markusdeli/Adobe-Lightroom-MIDI-Controller/3D-models/1MODE.stl

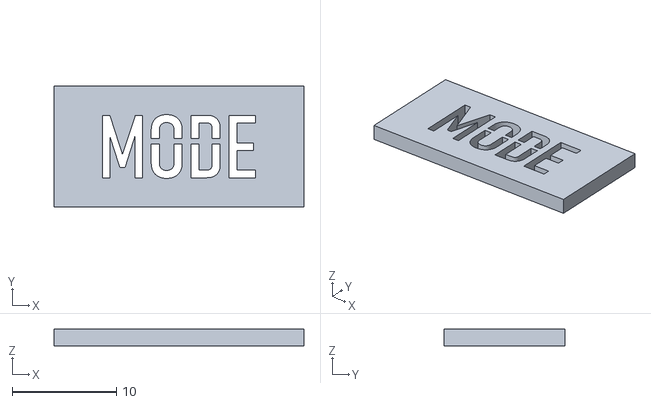
[picture p15: CAD file, 2021-11-03]
3D-models/1MODE.stl
24.0 x 11.6 x 1.60
