markusdeli/Adobe-Lightroom-MIDI-Controller/3D-models/DongleBottom.stl

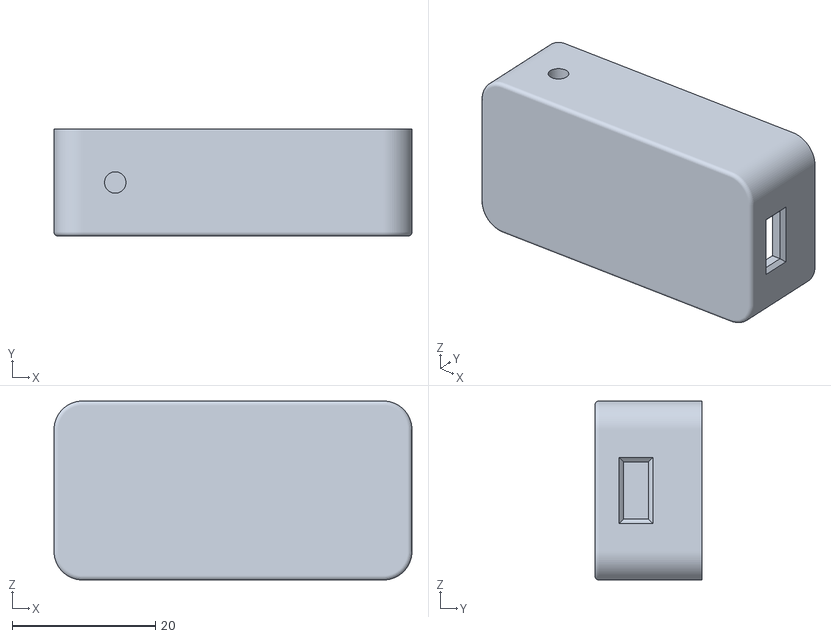
[picture p16: CAD file, 2021-11-03]
3D-models/DongleBottom.stl
50.0 x 15.0 x 25.0
