markusdeli/Adobe-Lightroom-MIDI-Controller/3D-models/color encoder.stl

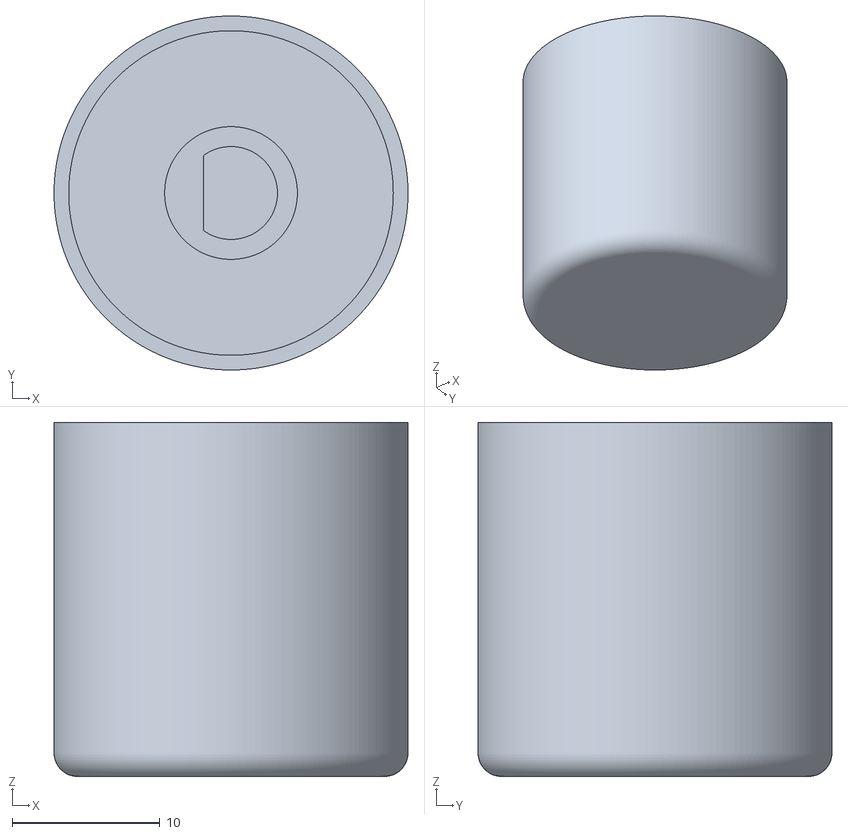
[picture p17: CAD file, 2021-11-03]
3D-models/color encoder.stl
24.0 x 24.0 x 24.0
