markusdeli/Adobe-Lightroom-MIDI-Controller/3D-models/kabelkammmidi.stl

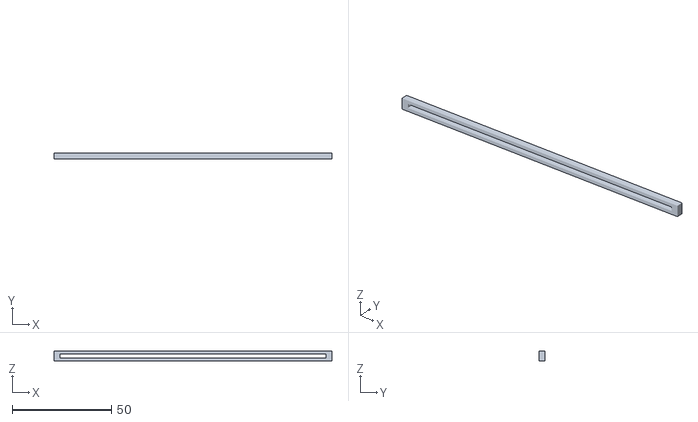
[picture p18: CAD file, 2021-11-03]
3D-models/kabelkammmidi.stl
140.0 x 3.00 x 5.00
