markusdeli/Adobe-Lightroom-MIDI-Controller/3D-models/1M2.stl

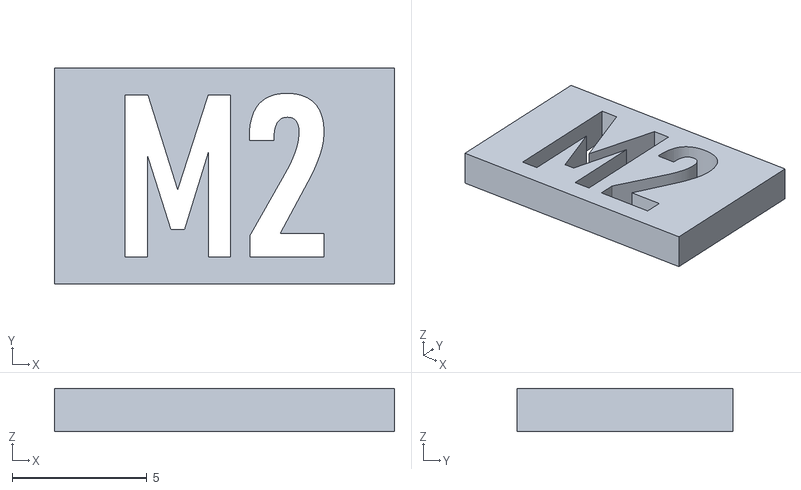
[picture p19: CAD file, 2021-11-03]
3D-models/1M2.stl
12.6 x 8.00 x 1.60
