markusdeli/Adobe-Lightroom-MIDI-Controller/3D-models/encoderfillMIDI.stl

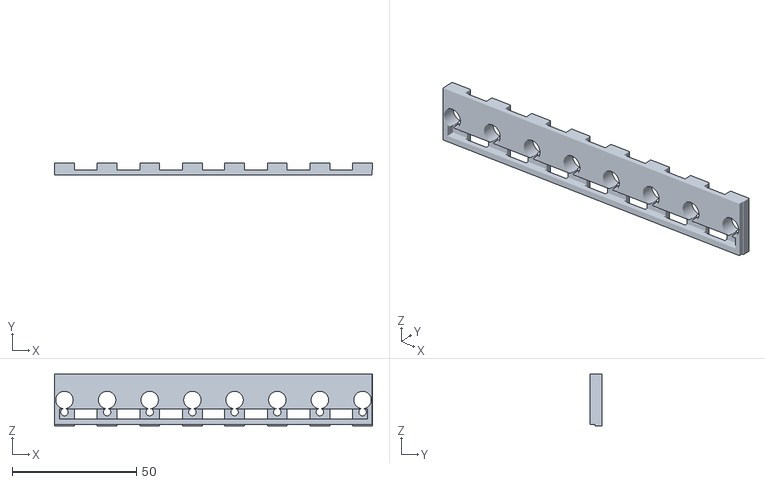
[picture p20: CAD file, 2021-11-03]
3D-models/encoderfillMIDI.stl
127.9 x 5.00 x 20.7
