markusdeli/Adobe-Lightroom-MIDI-Controller/3D-models/midicasetop.stl

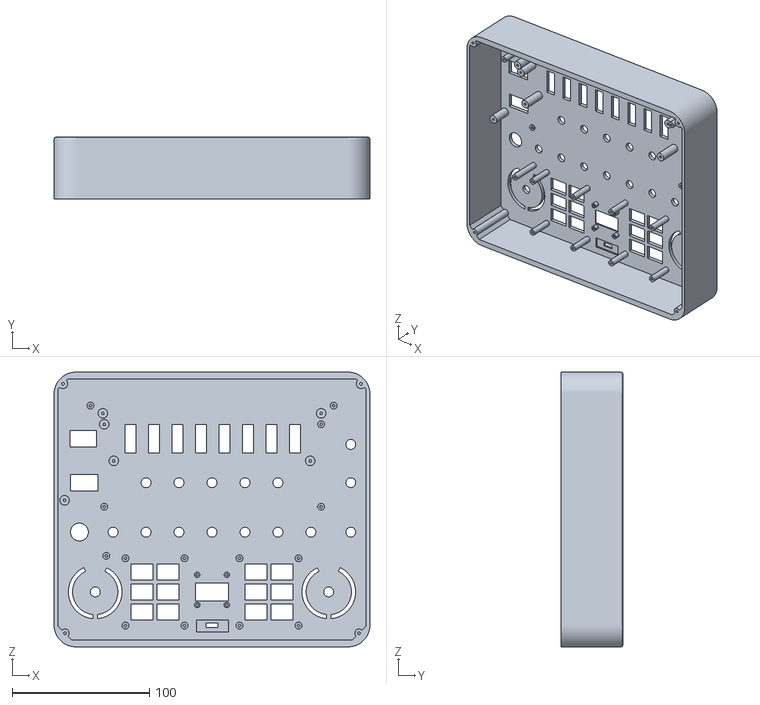
[picture p21: CAD file, 2021-11-03]
3D-models/midicasetop.stl
230.0 x 45.0 x 200.0
