markusdeli/Adobe-Lightroom-MIDI-Controller/3D-models/encoderbracketmidi.stl

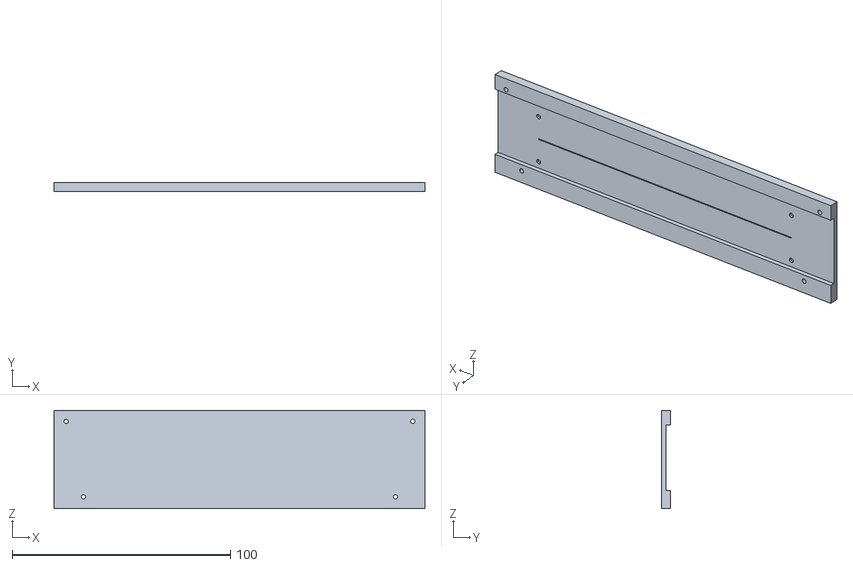
[picture p22: CAD file, 2021-11-03]
3D-models/encoderbracketmidi.stl
170.0 x 4.00 x 45.0
