markusdeli/Adobe-Lightroom-MIDI-Controller/3D-models/mouseshaftMIDI.stl

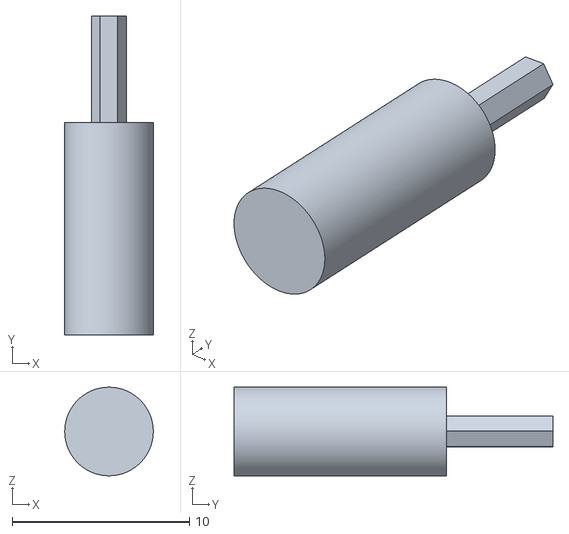
[picture p23: CAD file, 2021-11-03]
3D-models/mouseshaftMIDI.stl
5.00 x 18.0 x 5.00
