markusdeli/Adobe-Lightroom-MIDI-Controller/3D-models/DongleTop.stl

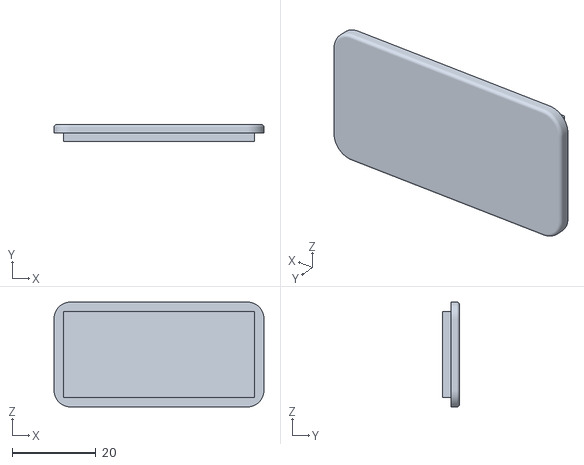
[picture p24: CAD file, 2021-11-03]
3D-models/DongleTop.stl
50.0 x 4.00 x 25.0
