markusdeli/Adobe-Lightroom-MIDI-Controller/3D-models/encoderKnobMaxiMIDI.stl

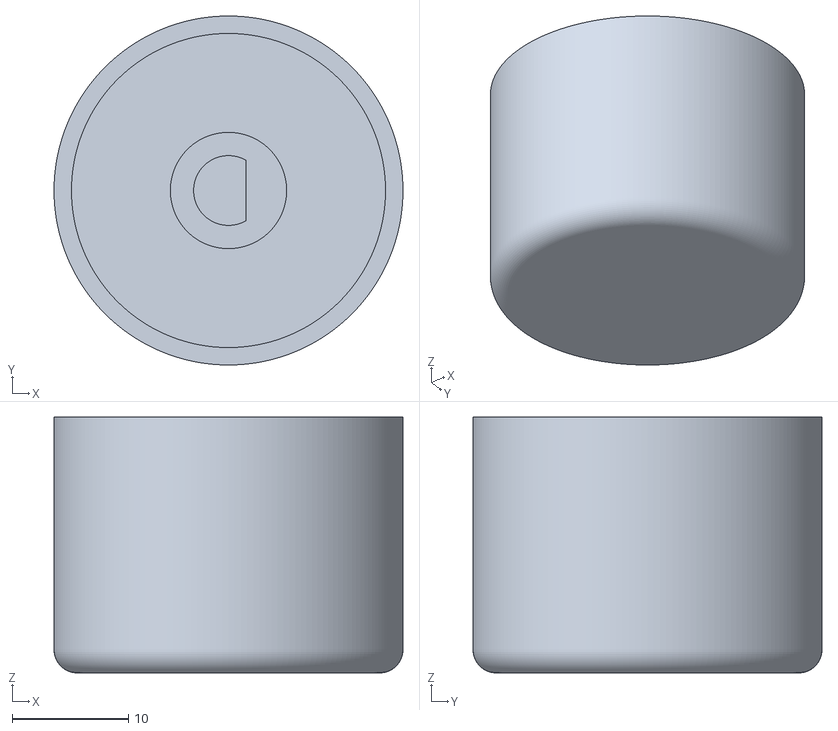
[picture p25: CAD file, 2021-11-03]
3D-models/encoderKnobMaxiMIDI.stl
30.0 x 30.0 x 22.0
