markusdeli/Adobe-Lightroom-MIDI-Controller/3D-models/midicontrollerv1.stl

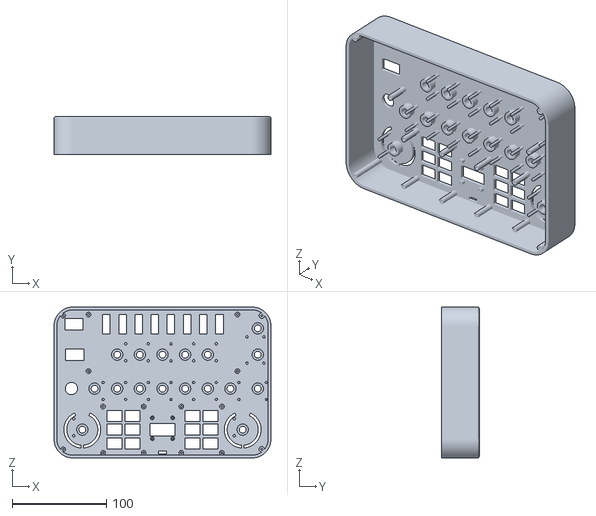
[picture p26: CAD file, 2021-11-03]
3D-models/midicontrollerv1.stl
230.0 x 40.0 x 160.0
