markusdeli/Adobe-Lightroom-MIDI-Controller/3D-models/b2.stl

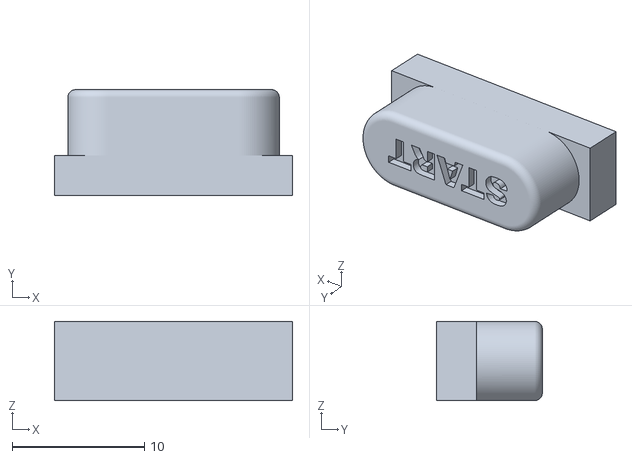
[picture p27: CAD file, 2021-11-03]
3D-models/b2.stl
18.0 x 8.00 x 6.00
