markusdeli/Adobe-Lightroom-MIDI-Controller/3D-models/stütze buttonMIDI.stl

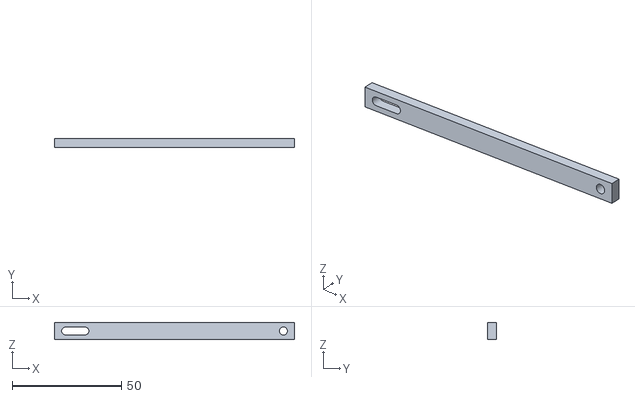
[picture p28: CAD file, 2021-11-03]
3D-models/stütze buttonMIDI.stl
110.0 x 4.00 x 8.00
