markusdeli/Adobe-Lightroom-MIDI-Controller/3D-models/buttonRotary.stl

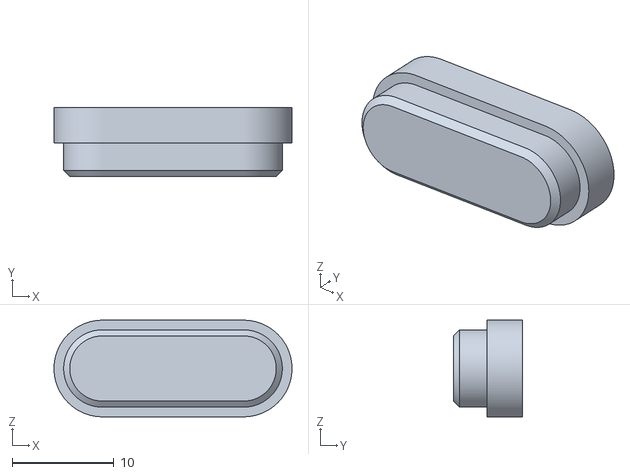
[picture p29: CAD file, 2021-11-03]
3D-models/buttonRotary.stl
23.4 x 6.80 x 9.50
