markusdeli/Adobe-Lightroom-MIDI-Controller/3D-models/buttonnichtsoklein.stl

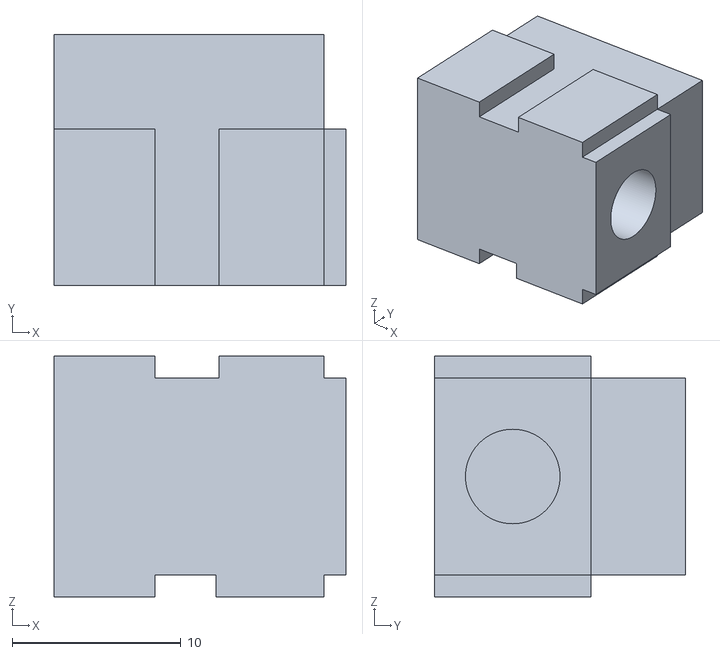
[picture p30: CAD file, 2021-11-03]
3D-models/buttonnichtsoklein.stl
17.3 x 14.9 x 14.3
