markusdeli/Adobe-Lightroom-MIDI-Controller/3D-models/encoderMAXIMIDI.stl

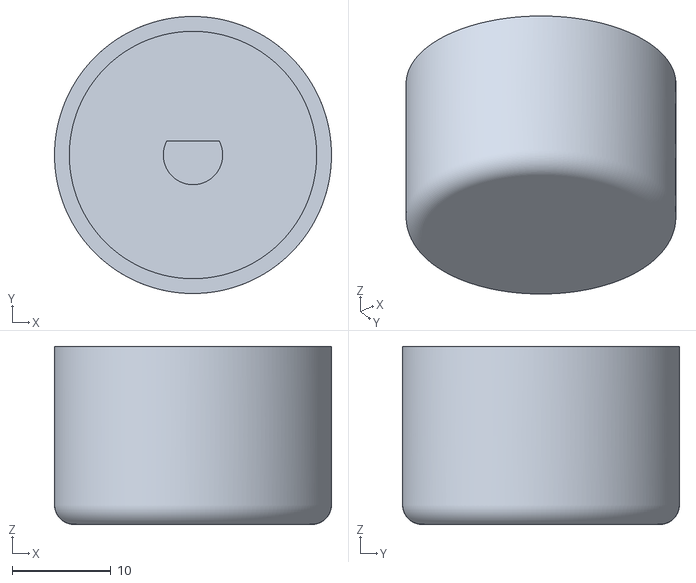
[picture p31: CAD file, 2021-11-03]
3D-models/encoderMAXIMIDI.stl
28.0 x 28.0 x 18.0
