markusdeli/Adobe-Lightroom-MIDI-Controller/3D-models/midiencoderwheel.stl

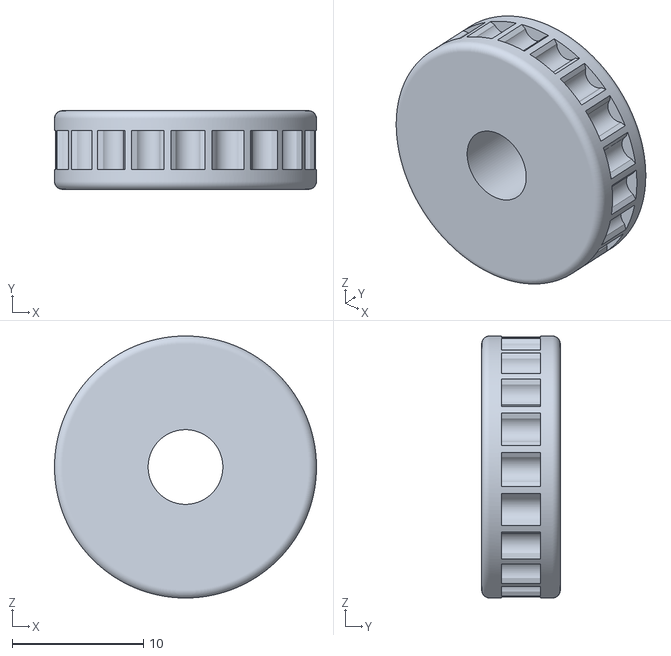
[picture p32: CAD file, 2021-11-03]
3D-models/midiencoderwheel.stl
20.0 x 6.00 x 20.0
