markusdeli/Adobe-Lightroom-MIDI-Controller/3D-models/buttonklein.stl

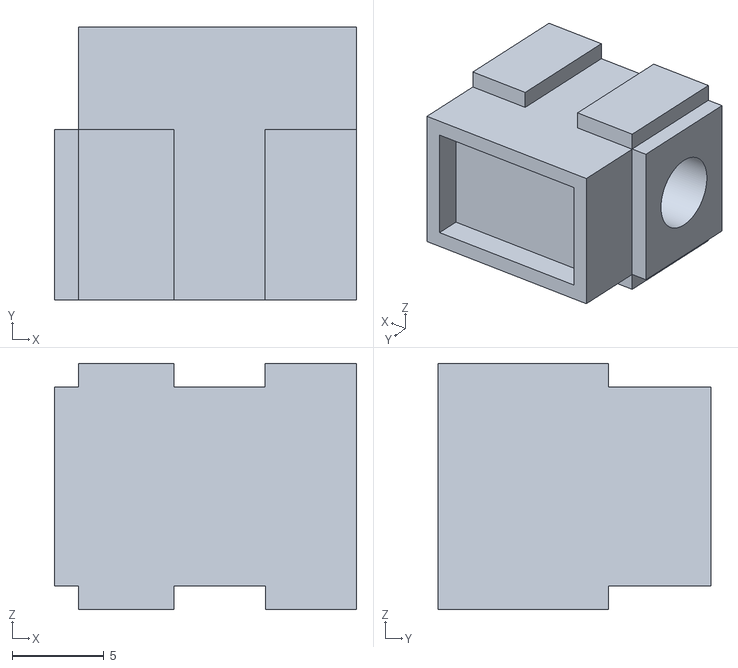
[picture p33: CAD file, 2021-11-03]
3D-models/buttonklein.stl
16.5 x 14.9 x 13.5
