markusdeli/Adobe-Lightroom-MIDI-Controller/3D-models/InlayTopMIDI.stl

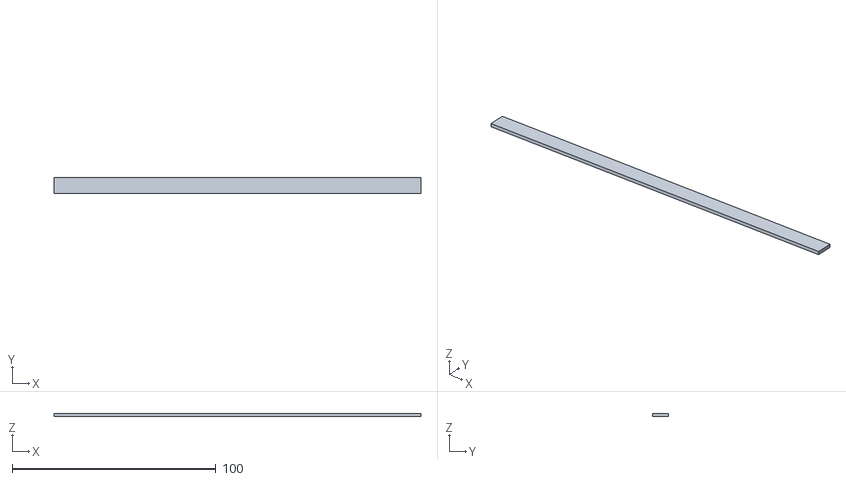
[picture p34: CAD file, 2021-11-03]
3D-models/InlayTopMIDI.stl
180.0 x 8.00 x 1.60
