markusdeli/Adobe-Lightroom-MIDI-Controller/3D-models/fillMIDIEnc.stl

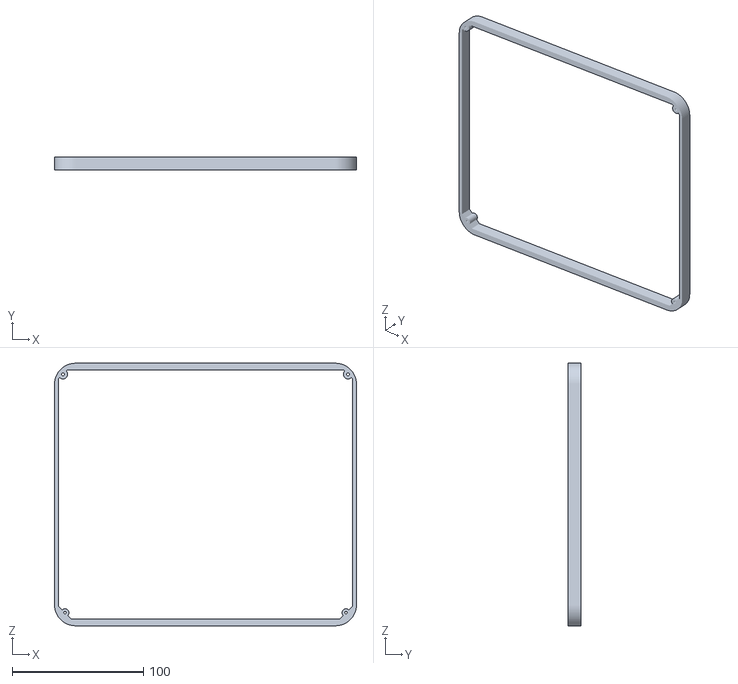
[picture p35: CAD file, 2021-11-03]
3D-models/fillMIDIEnc.stl
230.0 x 10.0 x 200.0
