markusdeli/Adobe-Lightroom-MIDI-Controller/3D-models/inlayWheelLEDMIDI.stl

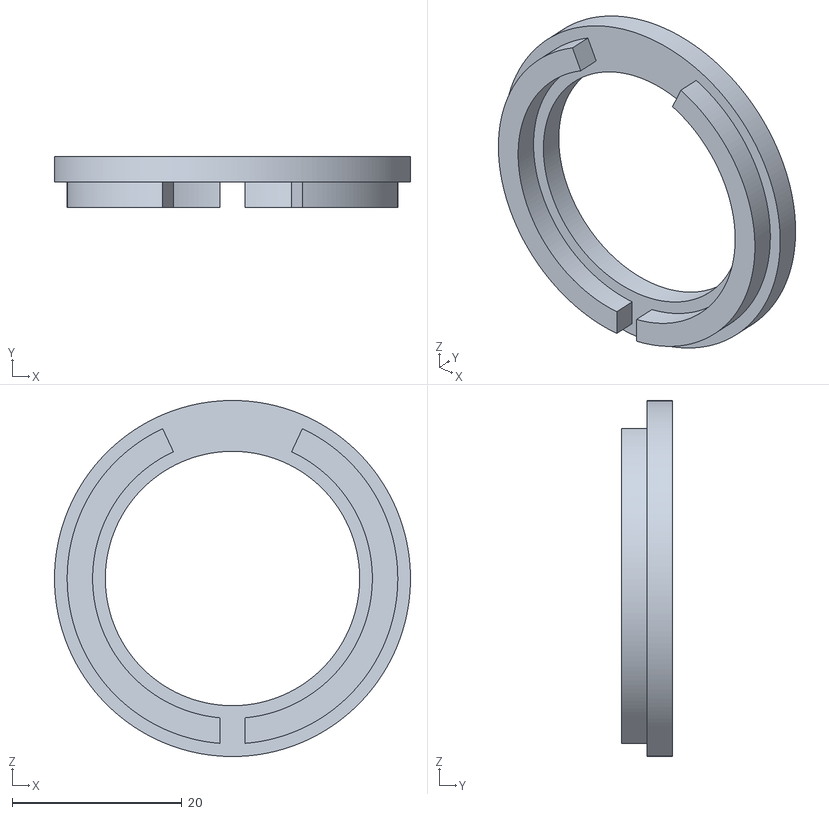
[picture p36: CAD file, 2021-11-03]
3D-models/inlayWheelLEDMIDI.stl
42.0 x 6.00 x 42.0
